fmalpartida/SAV-MAKER-I/3D models/Images/img_01.jpg

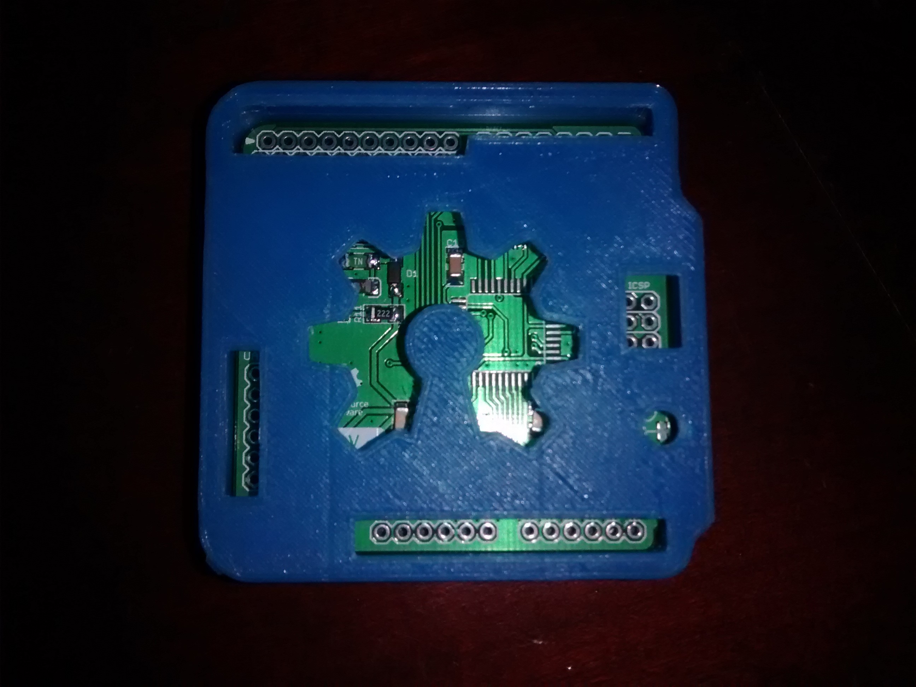
3D models/Images/img_01.jpg
