fmalpartida/SAV-MAKER-I/3D models/Images/img_02.jpg

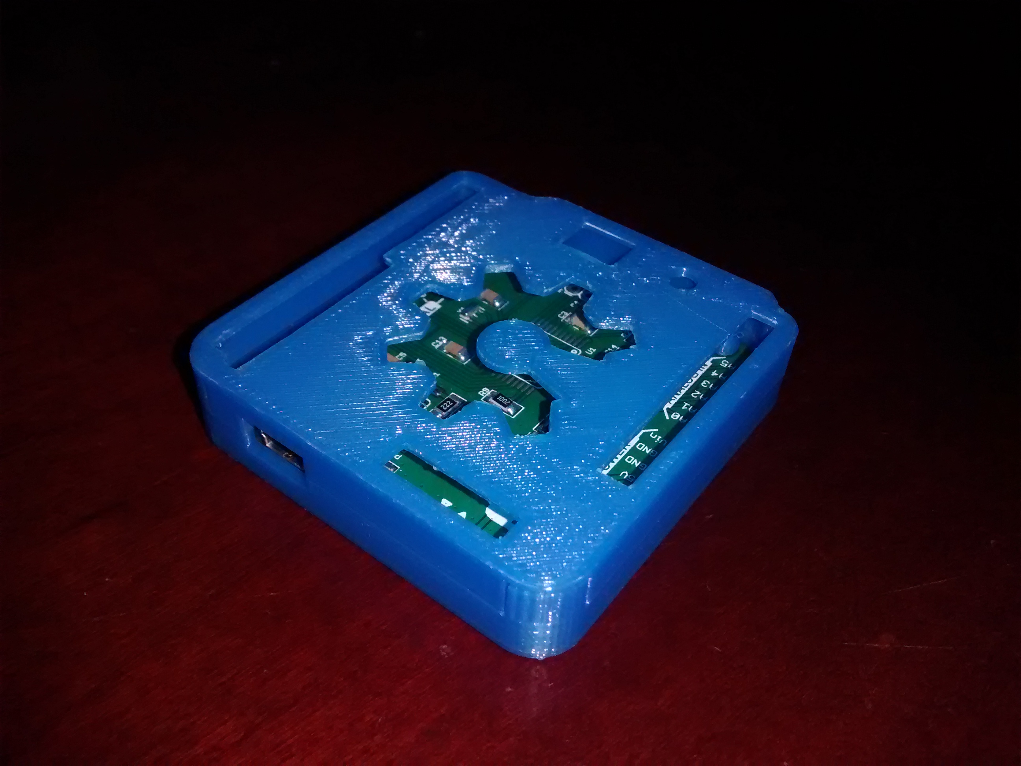
3D models/Images/img_02.jpg
