fmalpartida/SAV-MAKER-I/3D models/Images/IMG_20151128_170110620.jpg

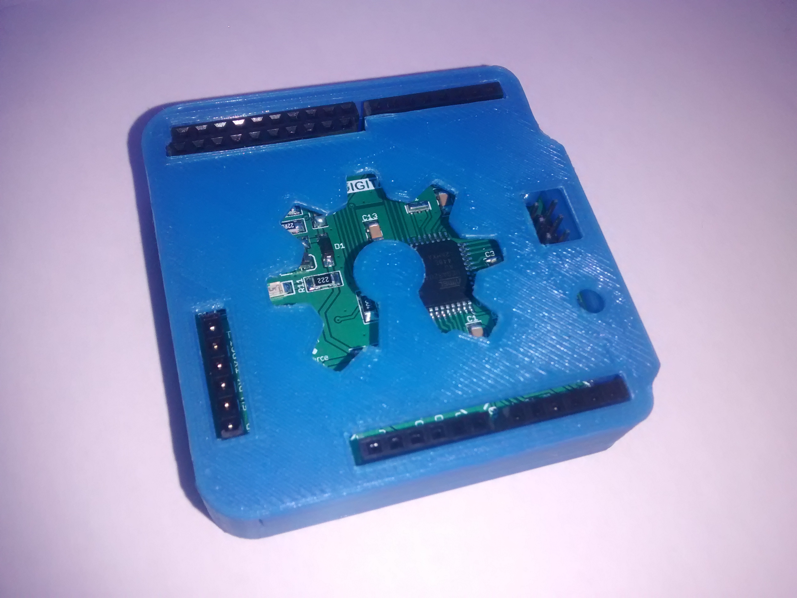
3D models/Images/IMG_20151128_170110620.jpg
