fmalpartida/SAV-MAKER-I/3D models/Images/IMG_20151128_170122520.jpg

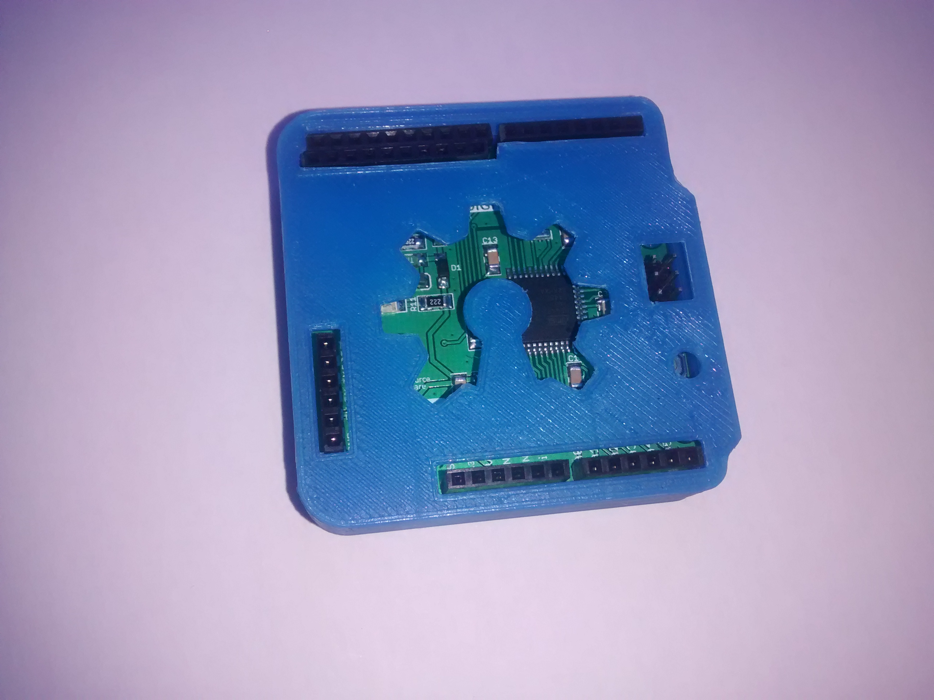
3D models/Images/IMG_20151128_170122520.jpg
