fmalpartida/SAV-MAKER-I/3D models/Images/SAV_M_I_CASE_v1.3.jpg

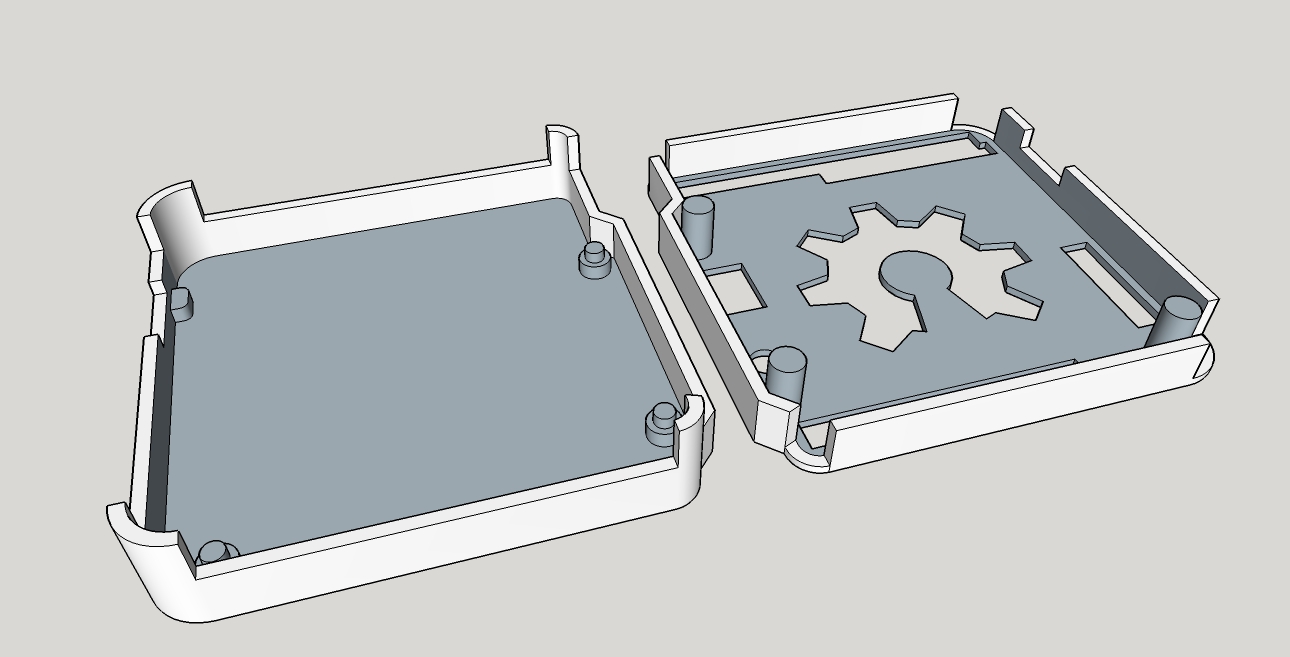
3D models/Images/SAV_M_I_CASE_v1.3.jpg
