fmalpartida/SAV-MAKER-I/artwork/board_Info.bmp

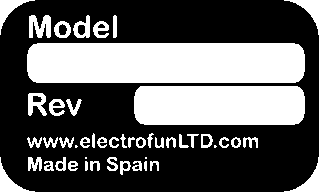
artwork/board_Info.bmp
