fmalpartida/SAV-MAKER-I/artwork/CERN-OHL-1.2.bmp

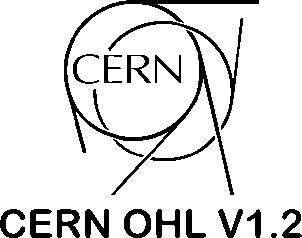
artwork/CERN-OHL-1.2.bmp
