fmalpartida/SAV-MAKER-I/artwork/SAVMakerI.bmp

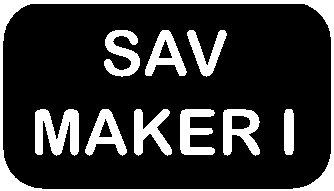
artwork/SAVMakerI.bmp
