fmalpartida/SAV-MAKER-I/images/Photos/1)Condensadores.jpg

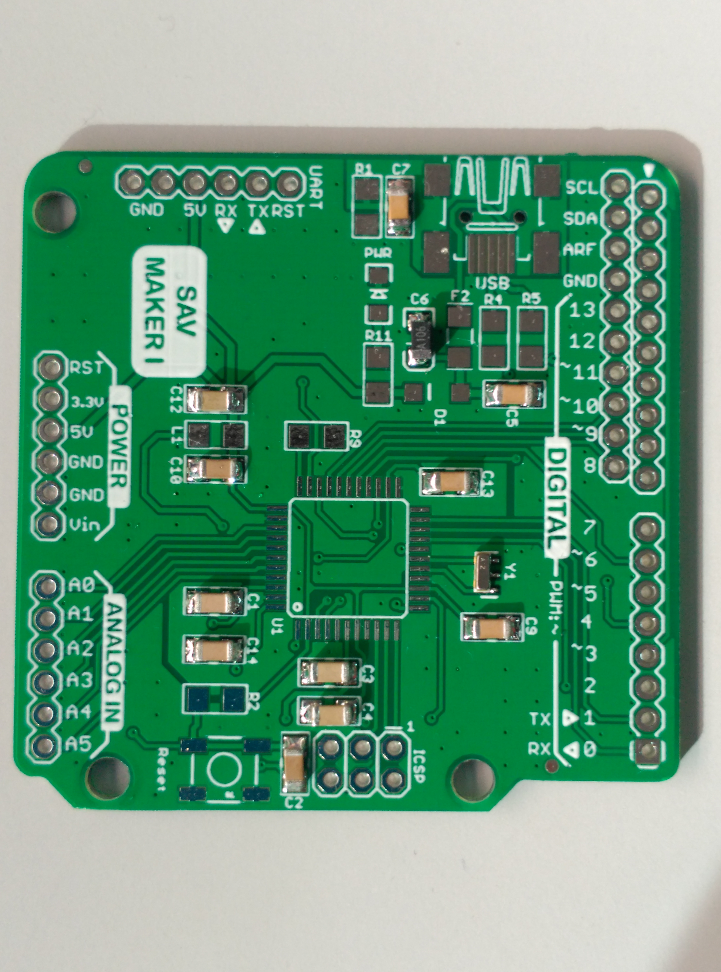
images/Photos/1)Condensadores.jpg
