fmalpartida/SAV-MAKER-I/images/Photos/2) + R2 R9 y R1.jpg

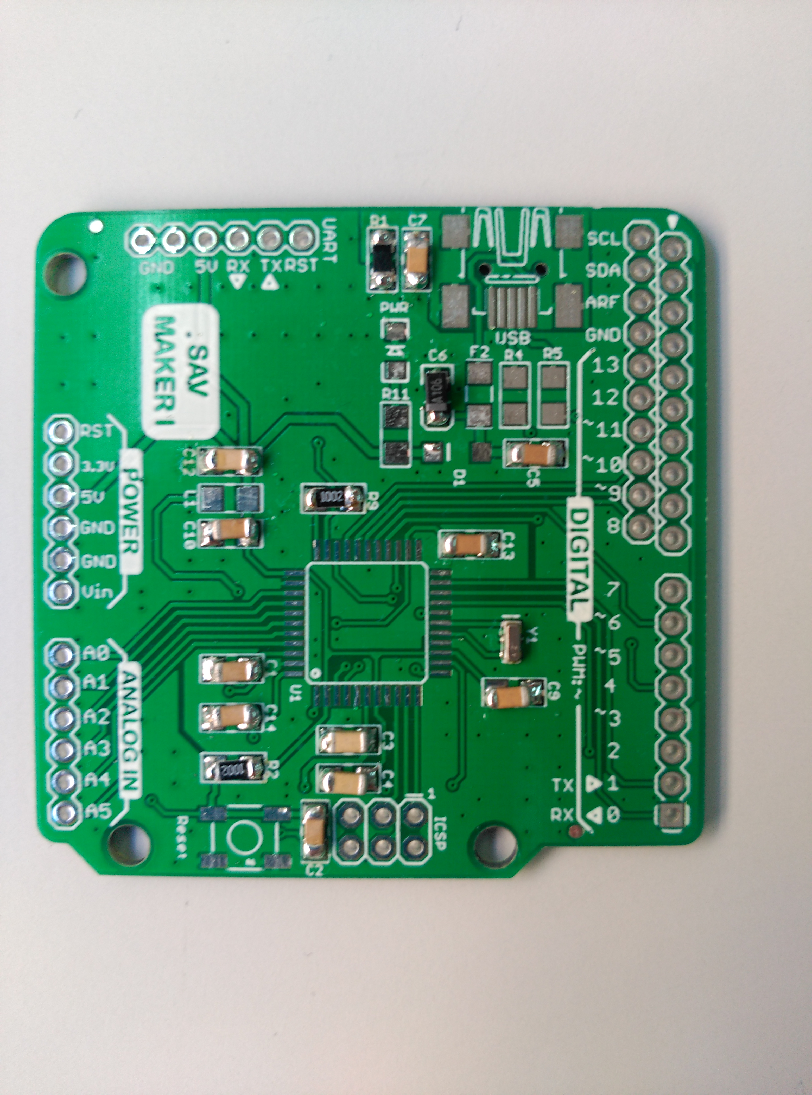
images/Photos/2) + R2 R9 y R1.jpg
