fmalpartida/SAV-MAKER-I/images/Photos/3)+ R4 R5 R11 y micro.jpg

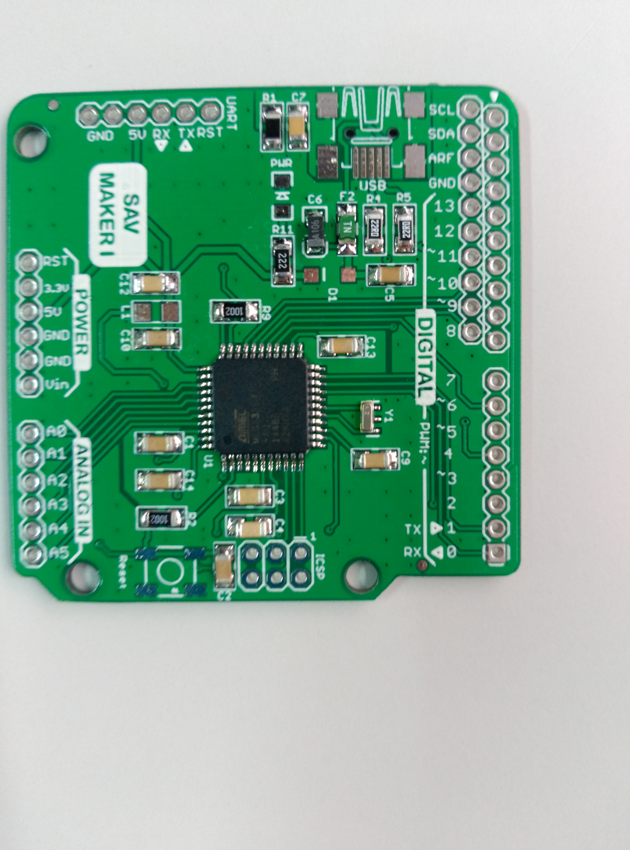
images/Photos/3)+ R4 R5 R11 y micro.jpg
