fmalpartida/SAV-MAKER-I/images/Photos/4) + MiniUSB.jpg

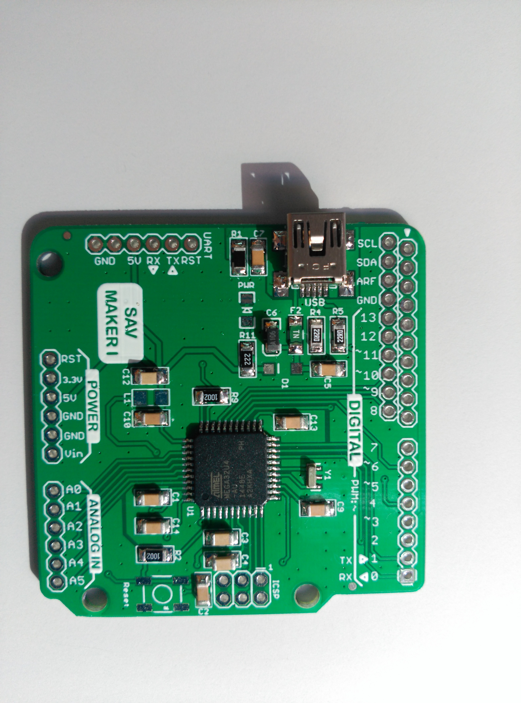
images/Photos/4) + MiniUSB.jpg
