fmalpartida/SAV-MAKER-I/images/Photos/6) + L1.jpg

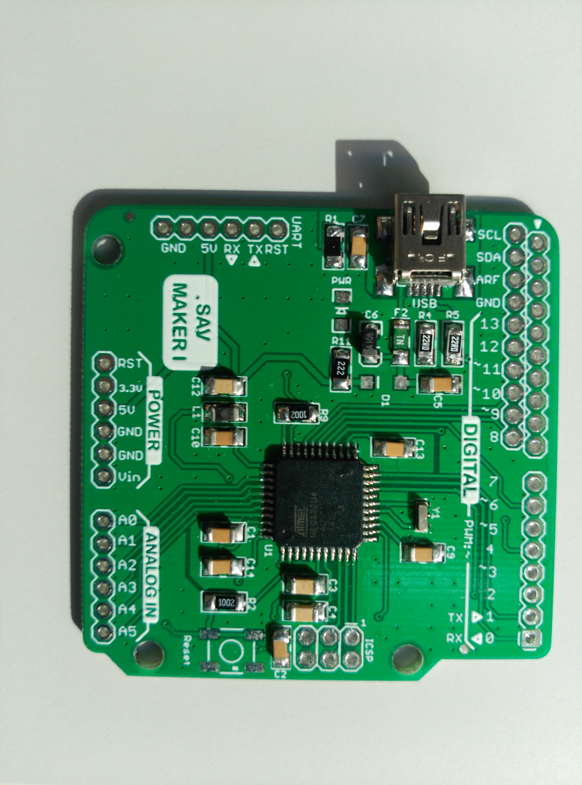
images/Photos/6) + L1.jpg
