fmalpartida/SAV-MAKER-I/images/Photos/8) + LED.jpg

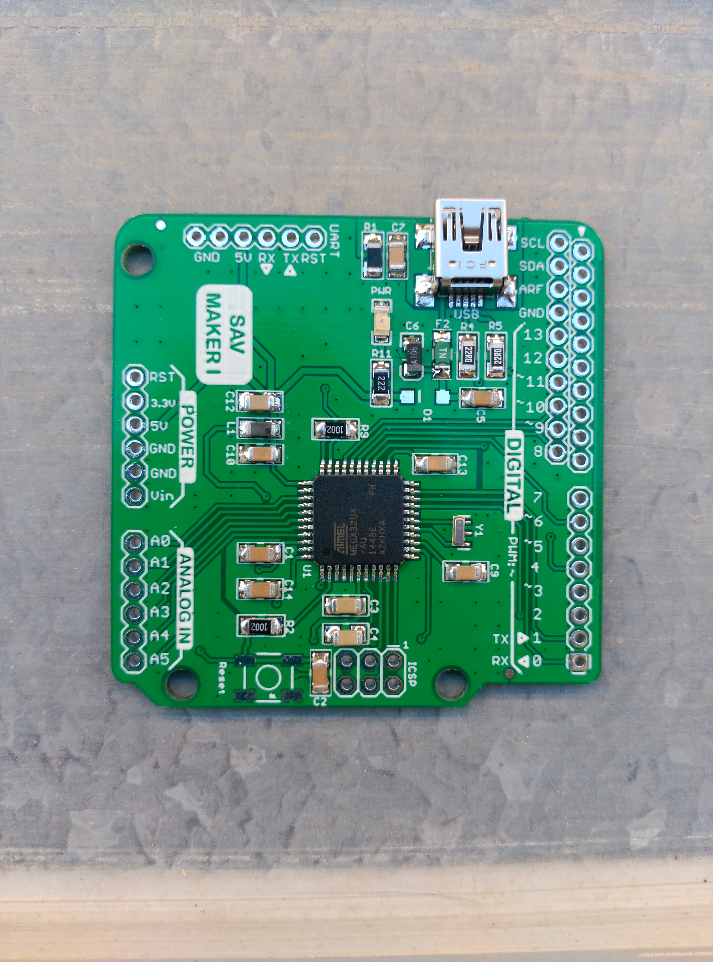
images/Photos/8) + LED.jpg
