fmalpartida/SAV-MAKER-I/images/Photos/9) +DIODE (D1).jpg

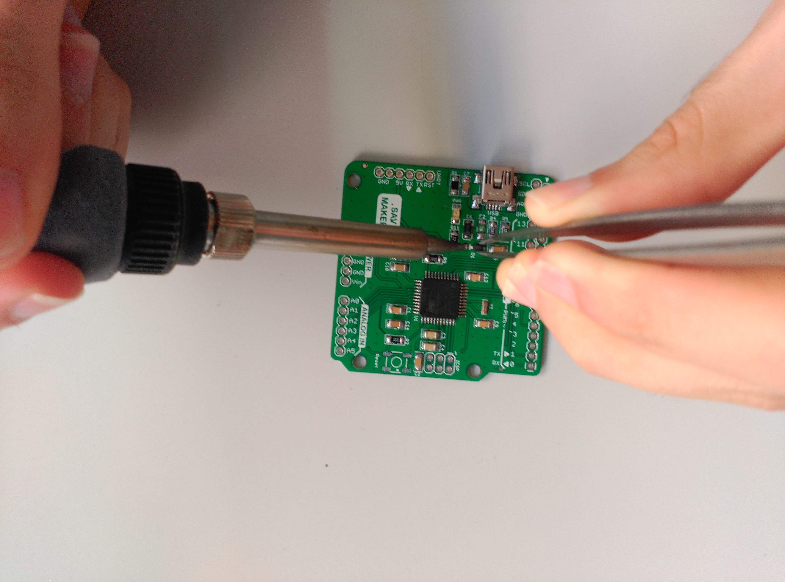
images/Photos/9) +DIODE (D1).jpg
