fmalpartida/SAV-MAKER-I/images/Photos/burn boot-loader on uno with Leonardo_bb (1).png

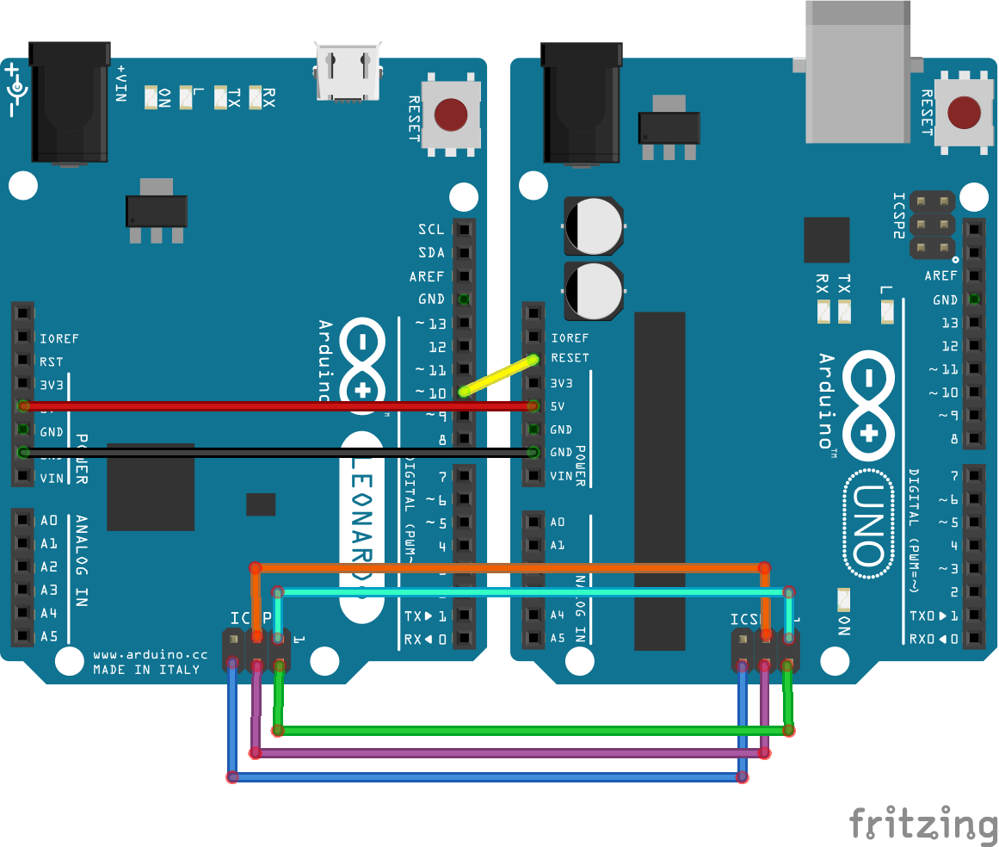
images/Photos/burn boot-loader on uno with Leonardo_bb (1).png
