fmalpartida/SAV-MAKER-I/assembly guide/Images/PlacingCapacitors1.JPG

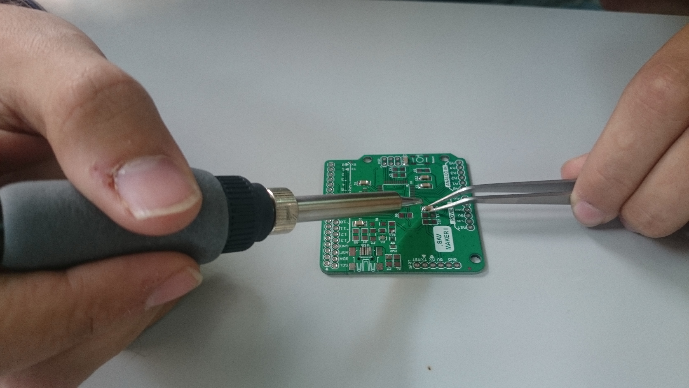
assembly guide/Images/PlacingCapacitors1.JPG
