fmalpartida/SAV-MAKER-I/assembly guide/Images/PlacingConectors.JPG

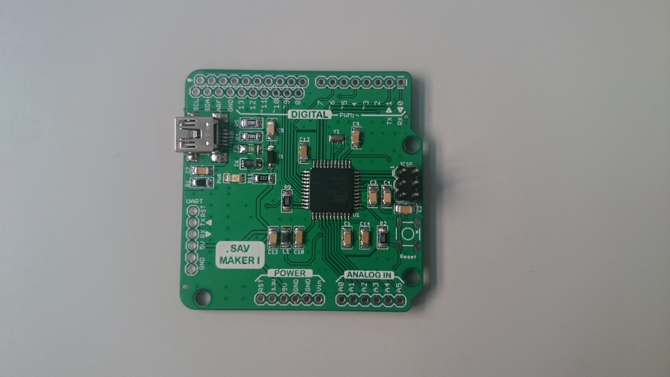
assembly guide/Images/PlacingConectors.JPG
