fmalpartida/SAV-MAKER-I/assembly guide/Images/PlacingDiode.JPG

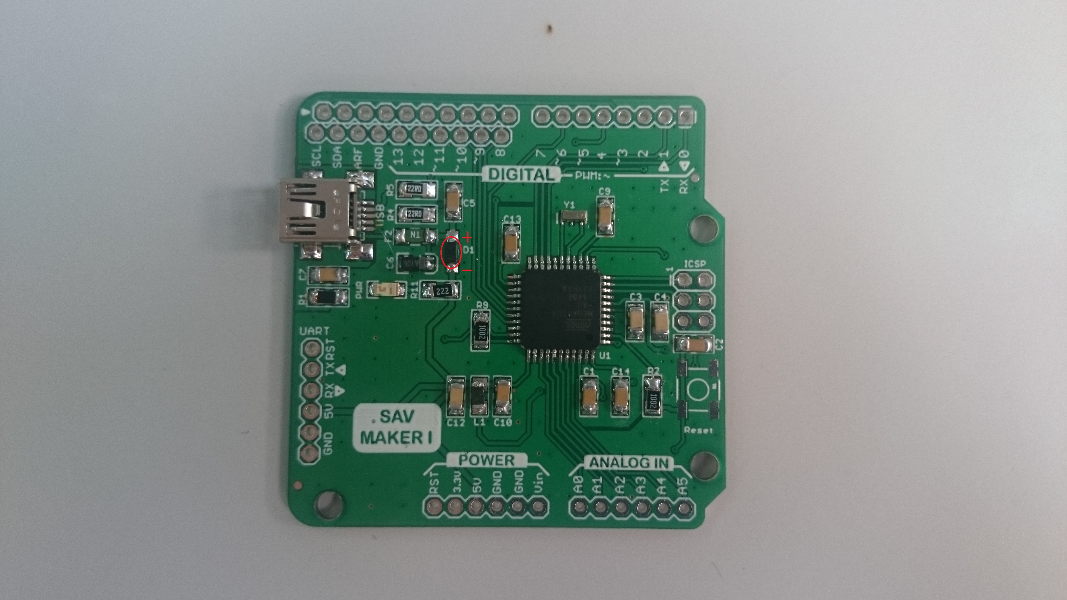
assembly guide/Images/PlacingDiode.JPG
