fmalpartida/SAV-MAKER-I/assembly guide/Images/PlacingL1F1.JPG

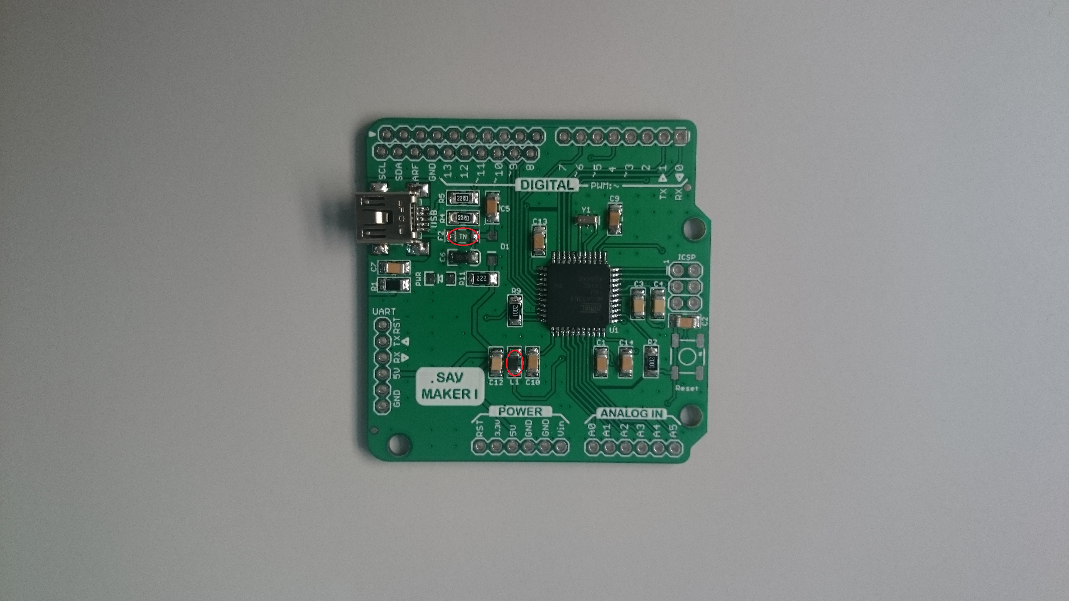
assembly guide/Images/PlacingL1F1.JPG
