fmalpartida/SAV-MAKER-I/assembly guide/Images/PlacingMicro.JPG

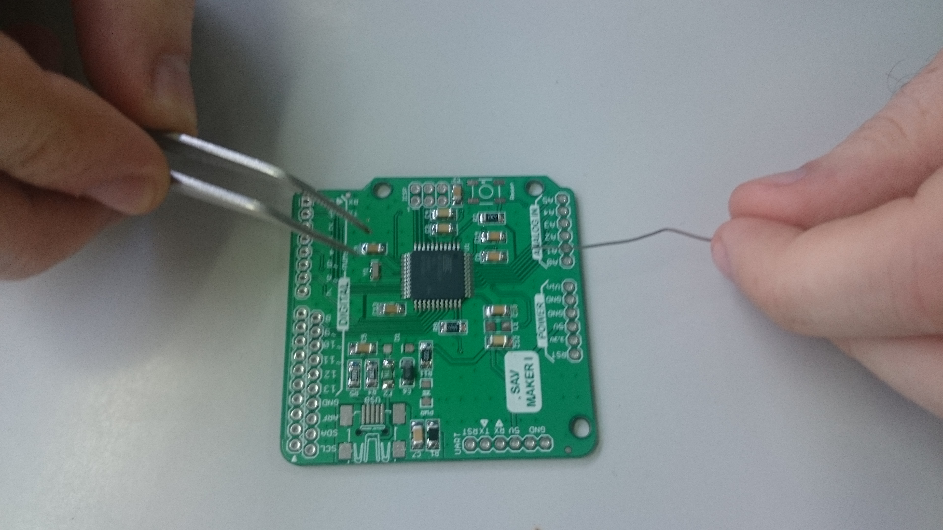
assembly guide/Images/PlacingMicro.JPG
