fmalpartida/SAV-MAKER-I/assembly guide/Images/PlacingResistances1.JPG

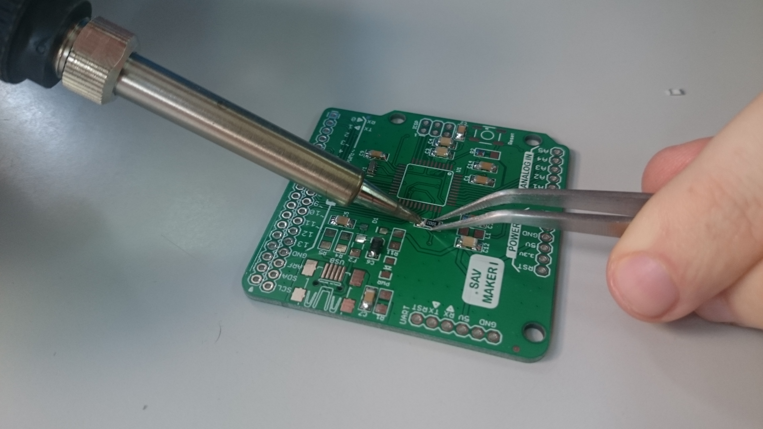
assembly guide/Images/PlacingResistances1.JPG
