fmalpartida/SAV-MAKER-I/assembly guide/Images/PlacingResistances2.JPG

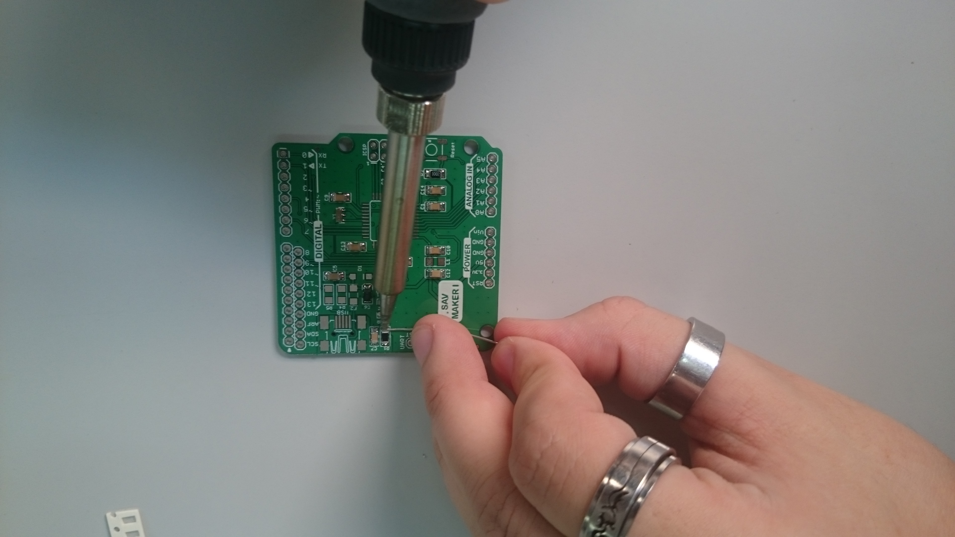
assembly guide/Images/PlacingResistances2.JPG
