fmalpartida/SAV-MAKER-I/assembly guide/Images/PlacingResistances3.JPG

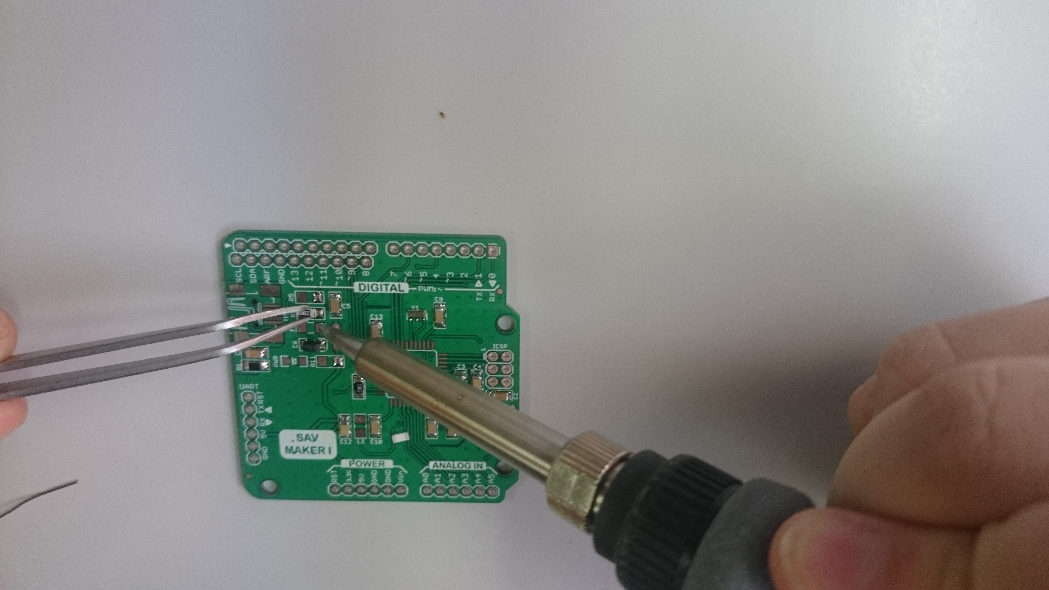
assembly guide/Images/PlacingResistances3.JPG
