fmalpartida/SAV-MAKER-I/assembly guide/Images/PlacingResonator.JPG

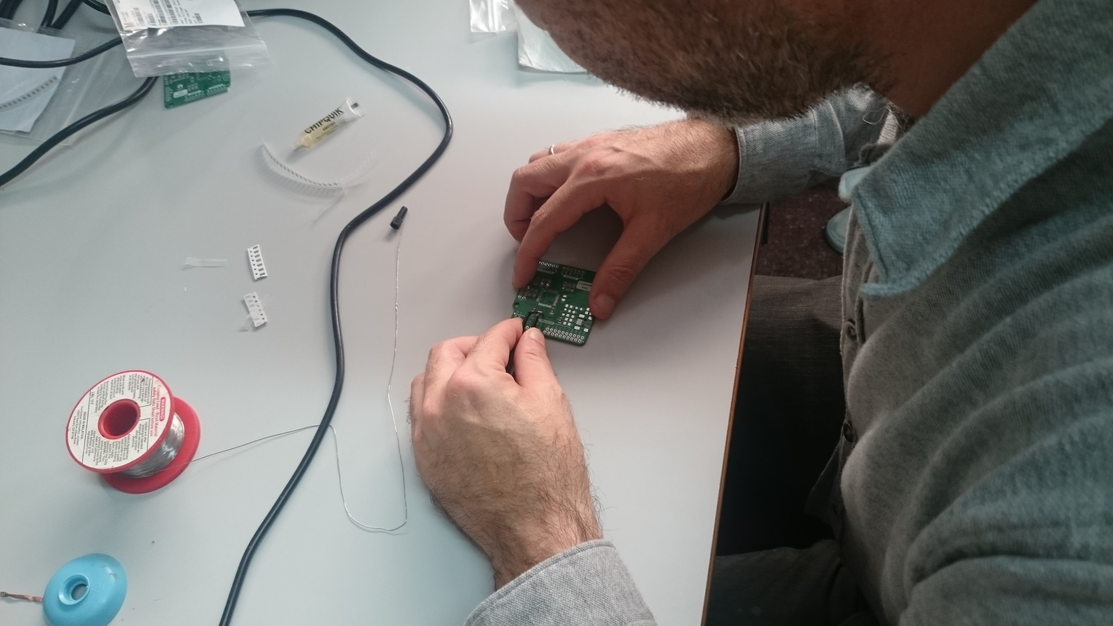
assembly guide/Images/PlacingResonator.JPG
