fmalpartida/SAV-MAKER-I/assembly guide/Images/PolarizedCapacitor.JPG

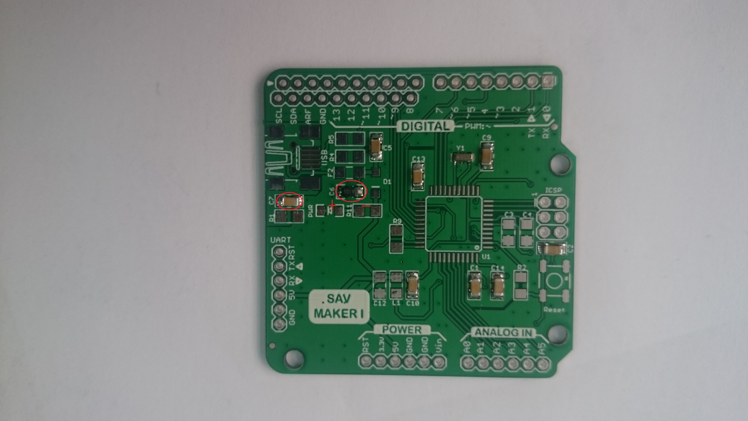
assembly guide/Images/PolarizedCapacitor.JPG
