fmalpartida/SAV-MAKER-I/assembly guide/Images/SAV-MAKER-I.jpg

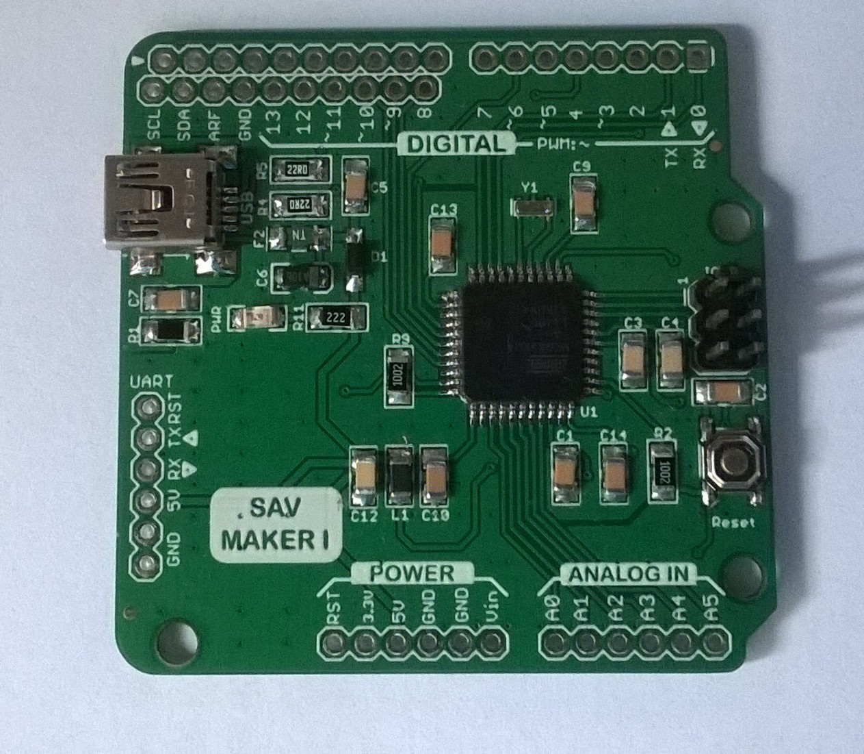
assembly guide/Images/SAV-MAKER-I.jpg
