fmalpartida/SAV-MAKER-I/assembly guide/Images/USBPlaced.JPG

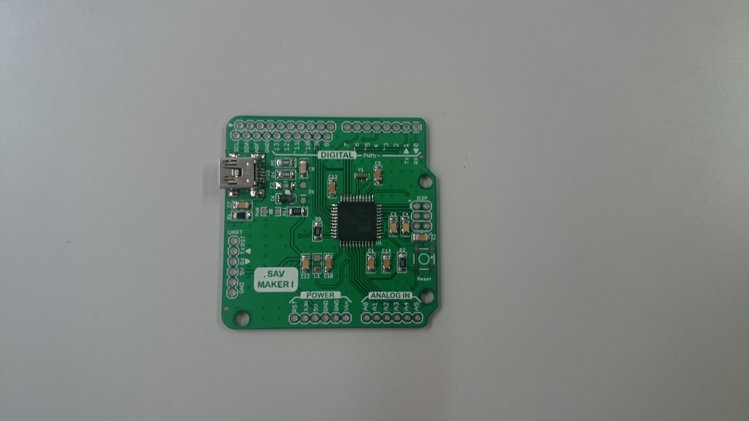
assembly guide/Images/USBPlaced.JPG
