fmalpartida/SAV-MAKER-I/images/Photos/5) Montaje L1.jpg

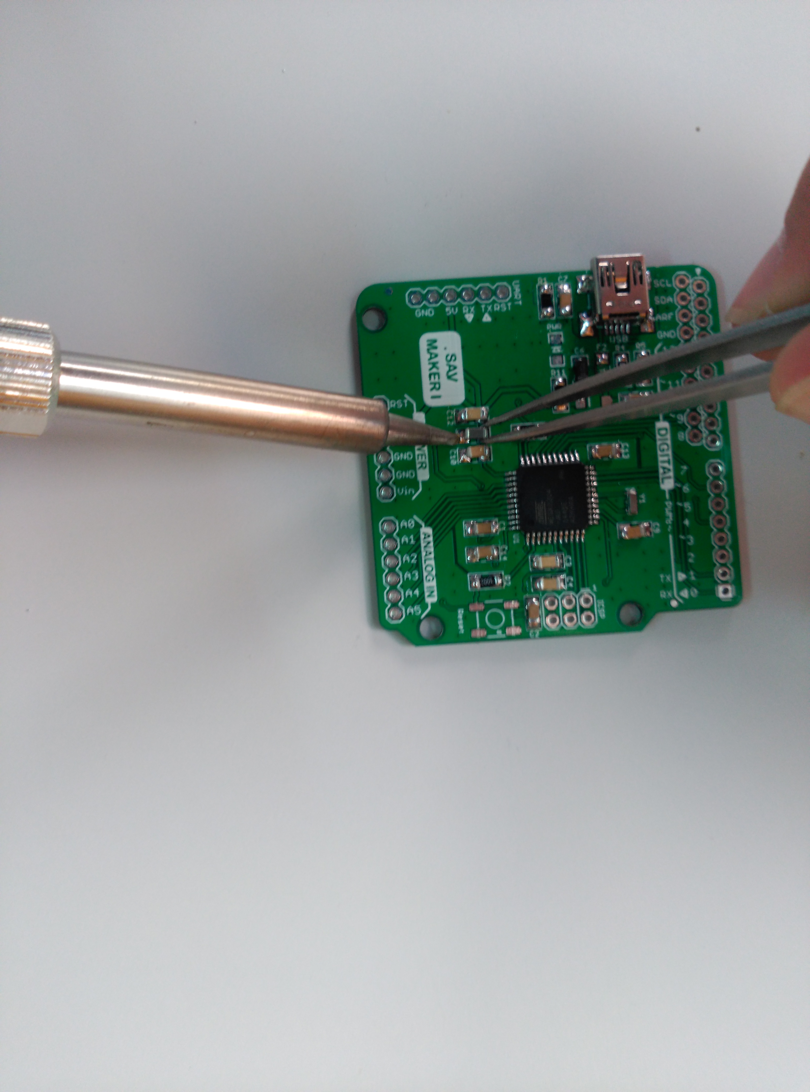
images/Photos/5) Montaje L1.jpg
