fmalpartida/SAV-MAKER-I/images/Photos/7) Montaje LED.jpg

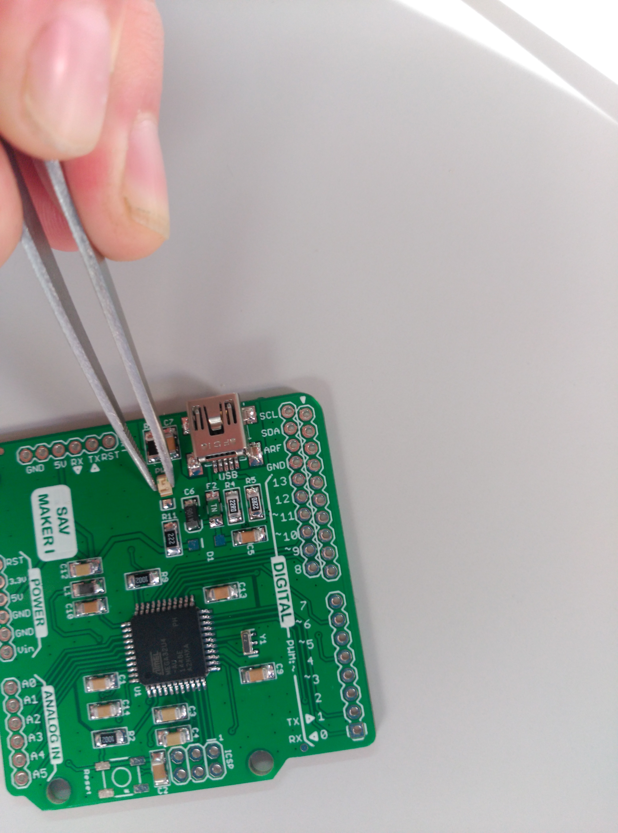
images/Photos/7) Montaje LED.jpg
