fmalpartida/SAV-MAKER-I/images/Photos/11) Montaje pines.jpg

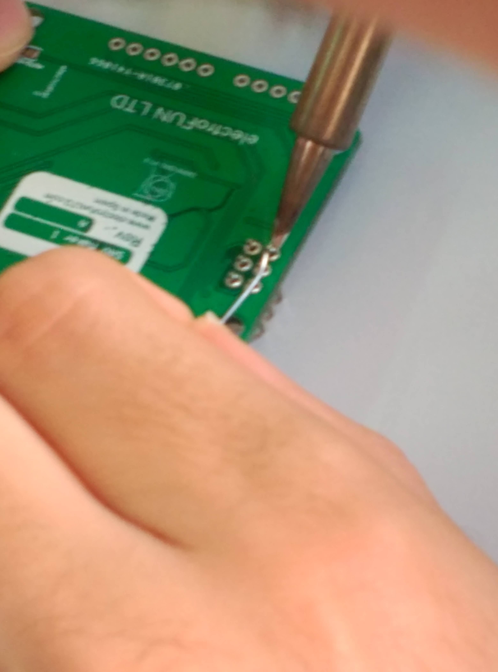
images/Photos/11) Montaje pines.jpg
