fmalpartida/SAV-MAKER-I/images/Photos/12) Montaje final.jpg

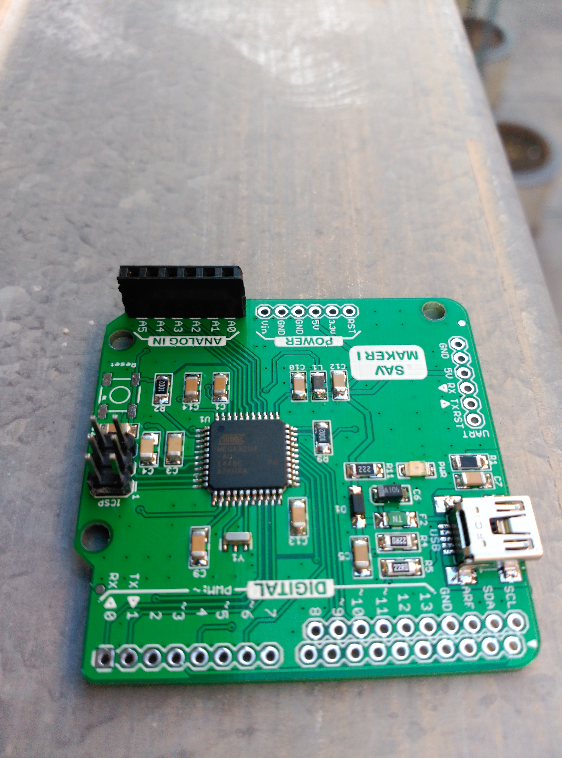
images/Photos/12) Montaje final.jpg
