fmalpartida/SAV-MAKER-I/images/RevB/SAV MAKER 1 RevB Bottom.png

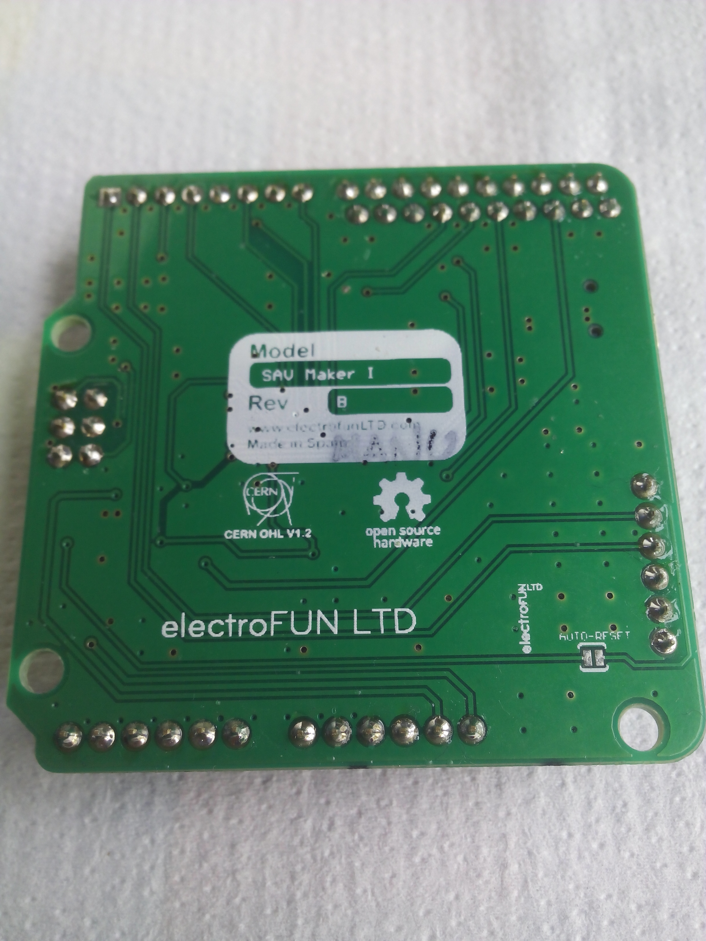
images/RevB/SAV MAKER 1 RevB Bottom.png
