fmalpartida/SAV-MAKER-I/images/RevB/SAV MAKER 1 RevB PCB.png

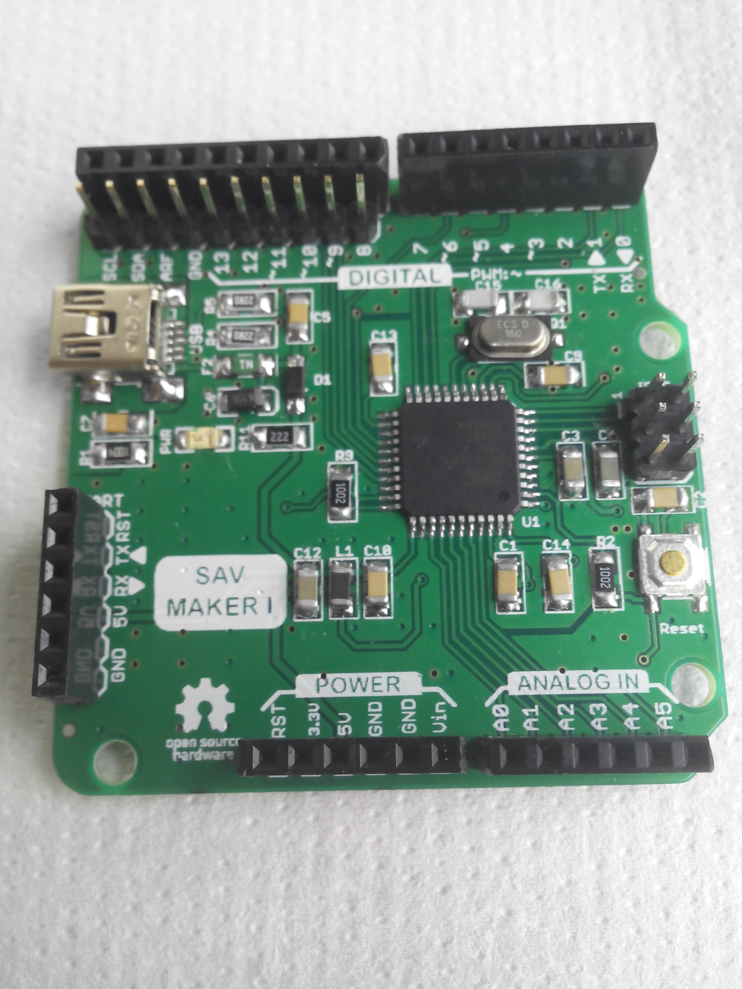
images/RevB/SAV MAKER 1 RevB PCB.png
