fmalpartida/SAV-MAKER-I/images/RevB/SAV MAKER I RevB top.png

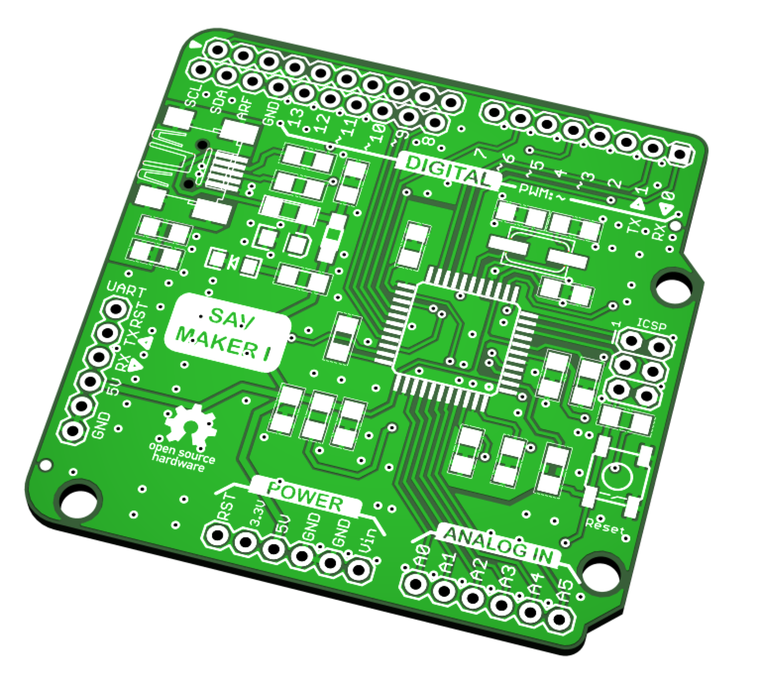
images/RevB/SAV MAKER I RevB top.png
