fmalpartida/SAV-MAKER-I/images/performance/3V_SUPPLE_NOISE.jpg

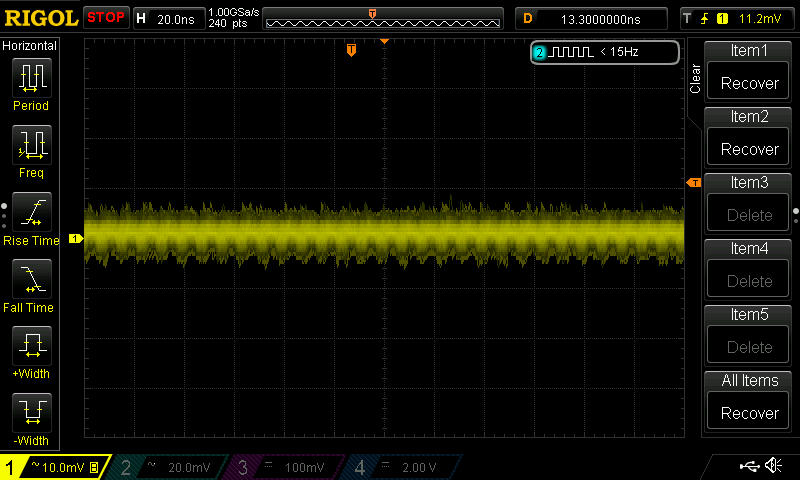
images/performance/3V_SUPPLE_NOISE.jpg
