fmalpartida/SAV-MAKER-I/images/performance/5V_SUPPLY.jpg

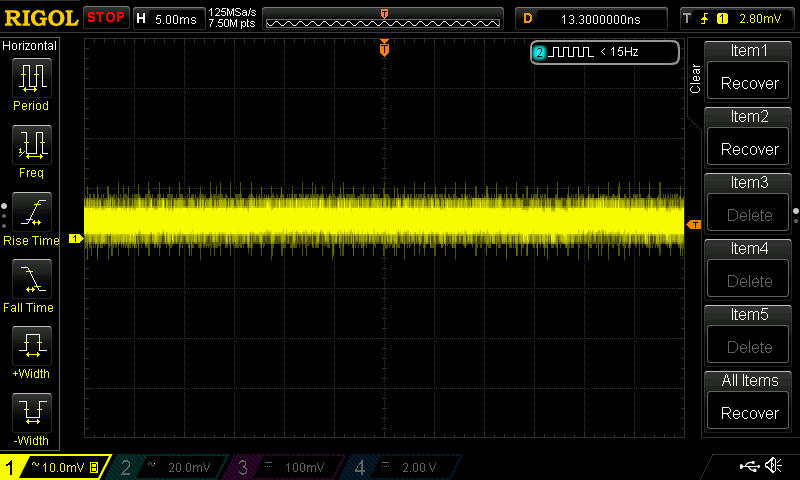
images/performance/5V_SUPPLY.jpg
