fmalpartida/SAV-MAKER-I/images/performance/ANALOG_SUPPLY.jpg

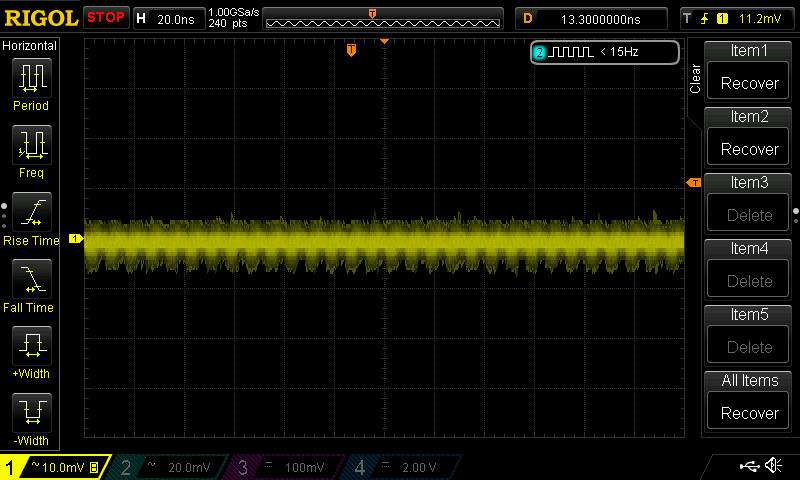
images/performance/ANALOG_SUPPLY.jpg
