fmalpartida/SAV-MAKER-I/images/performance/ANALOG_SUPPLY_NOISE.jpg

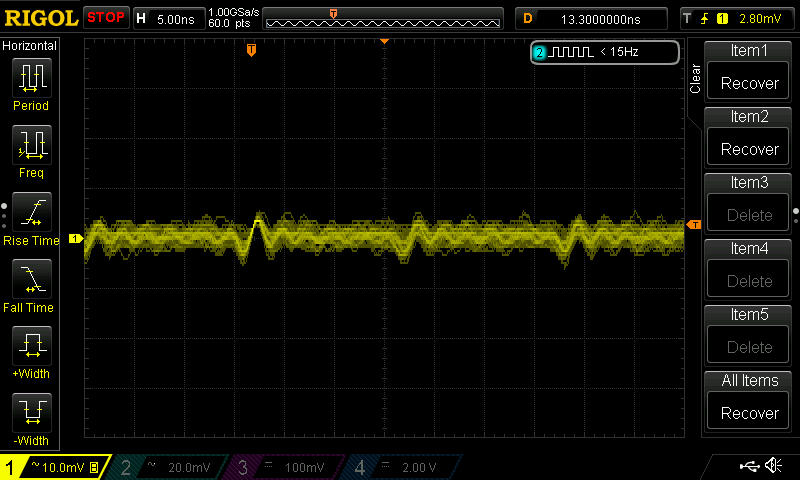
images/performance/ANALOG_SUPPLY_NOISE.jpg
