fmalpartida/SAV-MAKER-I/images/performance/IO_OUT_RISE.jpg

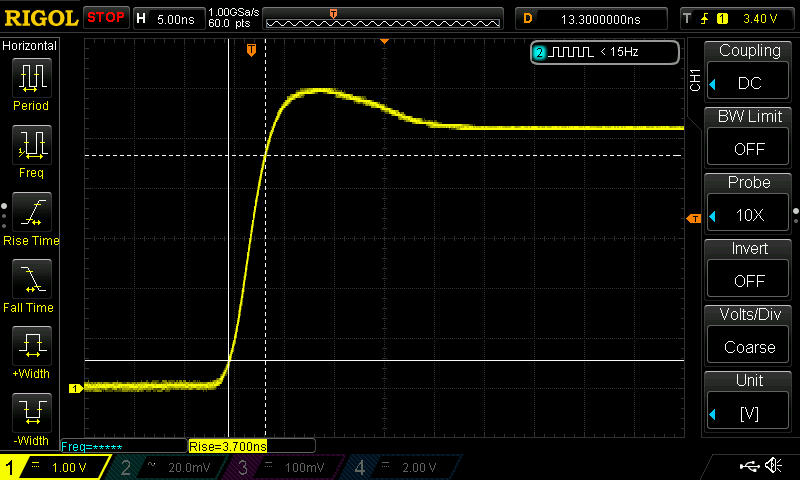
images/performance/IO_OUT_RISE.jpg
